htumanyan/navien/esphome/components/navien/navien_link.cpp

#include <cmath>

#include "esphome.h"
#include "esphome/core/log.h"
#include "navien.h"


namespace esphome {
namespace navien {

static const char *TAG = "navien.link";

NavienLink *NavienLink::get_instance(NavienUartI *uart) {
  static NavienLink *instance = nullptr;
  if (instance == nullptr) {
    if (uart == nullptr) {
      ESP_LOGE(TAG, "NavienLink UART adapter required on first get_instance call");
      return nullptr;
    }
    instance = new NavienLink(uart);
  } else if (uart != nullptr && instance->uart != uart) {
    ESP_LOGW(TAG, "Ignoring request to replace Navien UART adapter after initialization");
  }
  return instance;
}


bool NavienLink::seek_to_marker(){
  if (uart == nullptr) {
    return false;
  }
  uint8_t byte;

  int available = uart->available();
  for (int i = 0; i < available; i++){
    uart->peek_byte(&byte);
    if (byte == PACKET_MARKER)
      return true;
    
    uart->read_byte(&byte);
  }
  return false;
}


void NavienLink::parse_control_packet(){
  ESP_LOGV(TAG, "Got Control Packet => %d bytes", this->recv_buffer.hdr.len + HDR_SIZE);
  if (!this->other_navilink_installed
      && this->recv_buffer.hdr.len == NAVILINK_PRESENT[offsetof(HEADER, len)]
      && std::memcmp(this->recv_buffer.raw_data, NAVILINK_PRESENT, sizeof(NAVILINK_PRESENT)) == 0){
    /* This is a NAVILINK_PRESENT_PKT that wasn't sent by us, so anothe NaviLink is also hooked up */
    ESP_LOGW(TAG, "Detected NAVILINK_PRESENT packet from another NaviLink device, will stop sending NAVILINK_PRESENT packets until rebooted %d", sizeof(NAVILINK_PRESENT));
    this->other_navilink_installed = true;
  }
  //  Navien::print_buffer(this->recv_buffer.raw_data, this->recv_buffer.hdr.len + HDR_SIZE);
}
  
void NavienLink::parse_status_packet(){
  switch(this->recv_buffer.hdr.dst){
  case PACKET_DST_WATER:
    ESP_LOGD(TAG, "SRC:0x%02X B8: 0x%02X, B32: 0x%02X, r_enabled: 0x%02X",
             this->recv_buffer.hdr.src,
             this->recv_buffer.water.unknown_06,
             this->recv_buffer.water.unknown_32,
             this->recv_buffer.water.recirculation_enabled);
    for (uint8_t i = 0; i < NAVIEN_CASCADE_MAX; ++i)
      if (visitors_[i]) visitors_[i]->on_water(recv_buffer.water, recv_buffer.hdr.src);
    break;
  case PACKET_DST_GAS:
    ESP_LOGD(TAG, "SRC:0x%02X => Gas", this->recv_buffer.hdr.src);
    for (uint8_t i = 0; i < NAVIEN_CASCADE_MAX; ++i)
      if (visitors_[i]) visitors_[i]->on_gas(recv_buffer.gas, recv_buffer.hdr.src);
    break;
  }
}
  
void NavienLink::parse_packet(){
  uint8_t crc_c = 0x00;
  uint8_t crc_r = 0x00;

  //NavienLink::print_buffer(this->recv_buffer.raw_data, HDR_SIZE + this->recv_buffer.hdr.len + 1);
  crc_r = this->recv_buffer.raw_data[HDR_SIZE + this->recv_buffer.hdr.len];
  
  switch(this->recv_buffer.hdr.direction){
  case PACKET_DIR_STATUS: {
    uint16_t seed;
    if (this->recv_buffer.hdr.src == PACKET_SRC_STATUS) {
      seed = CHECKSUM_SEED_4B;
    } else {
      seed = CHECKSUM_SEED_62;
    }
    crc_c = NavienLink::checksum(this->recv_buffer.raw_data, HDR_SIZE + this->recv_buffer.hdr.len, seed);
    if (crc_c != crc_r){
      ESP_LOGE(TAG, "SRC:0x%02X Status Packet checksum error: 0x%02X (calc) != 0x%02X (recv), seed=0x%02X", this->recv_buffer.hdr.src, crc_c, crc_r, seed);
      NavienLink::print_buffer(this->recv_buffer.raw_data, HDR_SIZE + this->recv_buffer.hdr.len + 1);
      break;
    }
    parse_status_packet();
    break;
  }
  case PACKET_DIR_CONTROL:
  /**
   * The condition below was obsrved in cascade setup where there are lots of 
   * messages, apparently between Navien units and that have some other checksum algorithm that 
   * we're yet to discover. For now we simply ignore those packets. 
   */
    if (this->recv_buffer.hdr.src != PACKET_SRC_CONTROL) {
      ESP_LOGD(TAG, "Control packet from SRC:0x%02X - we don't know how to handle it yet", this->recv_buffer.hdr.src);
      return;
    }
    crc_c = NavienLink::checksum(this->recv_buffer.raw_data, HDR_SIZE + this->recv_buffer.hdr.len, CHECKSUM_SEED_62);
    if (crc_c != crc_r){
      ESP_LOGE(TAG, "SRC:0x%02X Control Packet checksum error: 0x%02X (calc) != 0x%02X (recv), seed=0x%02X", this->recv_buffer.hdr.src, crc_c, crc_r, CHECKSUM_SEED_62);
      this->on_error();
      NavienLink::print_buffer(this->recv_buffer.raw_data, HDR_SIZE + this->recv_buffer.hdr.len + 1);
      break;
    }
    parse_control_packet();
    break;
  }

  //  ESP_LOGV(TAG, "Calculated checksum over %d bytes => 0x%02X", HDR_SIZE + this->recv_buffer.hdr.len, crc);

}


void NavienLink::on_error() {
  ESP_LOGD(TAG, "Notifying visitors of communication error");
  for (uint8_t i = 0; i < NAVIEN_CASCADE_MAX; ++i) {
    if (visitors_[i]) {
      visitors_[i]->on_error();
    }
  }
}

  
void NavienLink::receive() {
  if (uart == nullptr) {
    ESP_LOGE(TAG, "UART pointer is null; skipping receive");
    return;
  }

  int available = uart->available();
  if (!available) {
    return;
  }

  ESP_LOGV(TAG, "%d bytes available", available);
  while (available) {
    switch (this->recv_state) {
      case INITIAL:
        if (this->seek_to_marker()) {
          this->recv_state = MARKER_FOUND;
          ESP_LOGV(TAG, "Marker Found");
          break;
        }
        // No marker found and no data left to read. Exit and wait for more bytes to come.
        return;
      case MARKER_FOUND:
        available = uart->available();
        if (available < HDR_SIZE) {
          ESP_LOGV(TAG, "Only %d bytes available - less than header size", available);
          return;
        }
        if (!uart->read_array(this->recv_buffer.raw_data, HDR_SIZE)) {
          ESP_LOGW(TAG, "Failed to read header");
          this->on_error();
          break;
        }
        this->recv_state = HEADER_PARSED;
        ESP_LOGV(TAG, "Parsed header. %d bytes of body left", this->recv_buffer.hdr.len);
        // fall through
      case HEADER_PARSED: {
        available = uart->available();

        // +1 here is for the checksum - it is in the last byte
        uint8_t len = this->recv_buffer.hdr.len + 1;
        if (available < len) {
          ESP_LOGV(TAG, "Only %d data bytes available - less than len", available);
          return;
        }
        if (!uart->read_array(this->recv_buffer.raw_data + HDR_SIZE, len)) {
          ESP_LOGW(TAG, "Failed to read %d bytes", len);
          this->on_error();
          break;
        }
        ESP_LOGV(TAG, "Got Packet => %d bytes", len + HDR_SIZE);

        if (!this->cmd_buffer.empty()) {
          // There are queued commands. Only send when we are sure the bus is clear to avoid collisions.
          if (!this->other_navilink_installed || std::memcmp(this->recv_buffer.raw_data, NAVILINK_PRESENT, 5) == 0) {
            NAVIEN_CMD cmd = cmd_buffer.back();
            cmd_buffer.pop_back();
            uart->write_array(cmd.buffer, cmd.len);
            // NavienLink::print_buffer(cmd.buffer, cmd.len);
          }
        } else {
          if (!this->other_navilink_installed) {
            // If there's no pending command, send a NAVILINK_PRESENT packet so the unit knows we're here.
            // When the unit is in an automatic recirculation mode, this tell is that we're controlling 
            // when it does and does not recirculate (and it triggers the "Recirculation settings must be 
            // configured through the NaviLink app" message on the unit's front panel when you try to
            // change the recirculation setting)
            uart->write_array(NAVILINK_PRESENT, sizeof(NAVILINK_PRESENT));
            // NavienLink::print_buffer(NAVILINK_PRESENT, sizeof(NAVILINK_PRESENT));
          }
        }

        // Navien::print_buffer(this->recv_buffer.raw_data, len + HDR_SIZE);
        this->parse_packet();
        available = uart->available();
        this->recv_state = INITIAL;
        break;
      }
    }
  }
}

void NavienLink::send_cmd(const uint8_t * buffer, uint8_t len, uint8_t tries){
  // Send multiple times by default. In experiments I've noticed
  // that sending once does not always work and that
  // the NaviLink sends the commands multiple times
  for (uint8_t i = 0; i < tries; i++) {
    this->cmd_buffer.push_front(NAVIEN_CMD(buffer, len));
  }
}
  
void NavienLink::send_turn_on_cmd(){
  this->send_cmd(TURN_ON_CMD, sizeof(TURN_ON_CMD));
}

void NavienLink::send_turn_off_cmd(){
  this->send_cmd(TURN_OFF_CMD, sizeof(TURN_OFF_CMD));
}

void NavienLink::send_hot_button_cmd(){
  this->send_cmd(HOT_BUTTON_PRESS_CMD, sizeof(HOT_BUTTON_PRESS_CMD));
  this->send_cmd(HOT_BUTTON_RELSE_CMD, sizeof(HOT_BUTTON_RELSE_CMD), 1);
}
  

void NavienLink::send_dhw_set_temp_cmd(float temp){
  uint8_t cmd[19];
  memcpy(cmd, DHW_SET_TEMP_CMD_TEMPLATE, sizeof(DHW_SET_TEMP_CMD_TEMPLATE));
  cmd[9] = temp * 2 + 0.5;
  cmd[18] = NavienLink::checksum(cmd, sizeof(DHW_SET_TEMP_CMD_TEMPLATE) - 1, CHECKSUM_SEED_62);

  NavienLink::print_buffer(cmd, sizeof(DHW_SET_TEMP_CMD_TEMPLATE));
  this->send_cmd(cmd, sizeof(DHW_SET_TEMP_CMD_TEMPLATE));
}

/**
 * Space-heating setpoint (combi / boiler units).
 *
 * Same 0x4F control packet as the DHW setpoint, with the temperature in
 * byte 10 instead of byte 9 (deg C * 2). Byte 9 stays 0x00, which the unit
 * treats as "leave DHW unchanged" - the mirror of DHW commands carrying 0x00
 * in byte 10, which never move the SH setpoint.
 *
 * Verified on an NCB-240/110H (device type NCB_H, f7 06 framing): commands
 * for 160.7 F, 158.9 F and 156.2 F were each followed by the unit reporting
 * that value in the gas packet's sh_set_temp. Byte 10 is the slot tankless
 * units always leave 0x00.
 */
void NavienLink::send_sh_set_temp_cmd(float temp){
  uint8_t cmd[19];
  memcpy(cmd, DHW_SET_TEMP_CMD_TEMPLATE, sizeof(DHW_SET_TEMP_CMD_TEMPLATE));
  cmd[10] = temp * 2 + 0.5;
  cmd[18] = NavienLink::checksum(cmd, sizeof(DHW_SET_TEMP_CMD_TEMPLATE) - 1, CHECKSUM_SEED_62);

  NavienLink::print_buffer(cmd, sizeof(DHW_SET_TEMP_CMD_TEMPLATE));
  this->send_cmd(cmd, sizeof(DHW_SET_TEMP_CMD_TEMPLATE));
}

void NavienLink::send_scheduled_recirculation_on_cmd(){
  this->send_cmd(SCHEDULED_RECIRC_ON_CMD, sizeof(SCHEDULED_RECIRC_ON_CMD));
}

void NavienLink::send_scheduled_recirculation_off_cmd(){
  this->send_cmd(SCHEDULED_RECIRC_OFF_CMD, sizeof(SCHEDULED_RECIRC_OFF_CMD));
}

/**
 * Convert flow units to liters/min values
 * flow is reported as 0.1 liter units.
 */
float NavienLink::flow2lpm(uint8_t f){
  return (float)f / 10.f;
}
  
/**
 * Convert flow units to GPM values
 * flow is reported as 0.1 liter units.
 * we're calculating flow in liters/min and then
 * converting to gallons resulting in GPM (Gallons Per Min)
 */
float NavienLink::flow2gpm(uint8_t f){
  return  (float)f / 10.f / 3.785f;
}

float NavienLink::t2c(uint8_t c){
  return (float)c / 2.f;
}

float NavienLink::ot2c(uint8_t c){
  // Value when no probe is connected.
  // Decodes to right at low end of many 10k thermistors (-30C) so probably min reportable?
  if (c == 0x9E) {
    return NAN;
  }
  float sign = c & 0x80 ? -1 : 1;
  float mag = c & 0x7F;
  return sign * mag;
}
  
uint8_t NavienLink::t2f(uint8_t c){
  float f = c;

  f /= 2;

  f = f * 9.f / 5.f + 32.f;

  return (uint8_t)round(f);
}

  
void NavienLink::print_buffer(const uint8_t *data, size_t length) {
   char hex_buffer[100];
   hex_buffer[(3 * 32) + 1] = 0;
   for (size_t i = 0; i < length; i++) {
     size_t offset = 3 * (i % 32);
     snprintf(&hex_buffer[offset], sizeof(hex_buffer) - offset, "%02X ", data[i]);
     if (i % 32 == 31) {
       ESP_LOGI(TAG, "   %s", hex_buffer);
     }
   }
   if (length % 32) {
     // null terminate if incomplete line
     hex_buffer[3 * (length % 32) + 2] = 0;
     ESP_LOGI(TAG, "   %s", hex_buffer);
   }
 }

  
uint8_t NavienLink::checksum(const uint8_t * buffer, uint8_t len, uint16_t seed){  
  uint16_t result;

  if (len < 2) {
    result = 0x00;
  }
  else {
    result = 0xff;

    for (uint i = 0; i < len; i++){
      result = result << 1;

      if (result > 0xff){
	result = (result & 0xff) ^ seed;
      }

      // this is important!!
      // the checksum is calculated
      // based on the lower byte, i.e.
      // only the lower byte is XOR-ed
      result = ((uint8_t)result) ^ (uint16_t)buffer[i];
    }
  }
  return result;
}


  
}  // namespace navien
}  // namespace esphome
