htumanyan/navien/esphome/components/navien/navien_link_esp.h

#pragma once

// NavienLinkEsp has been deprecated. This header remains for backward compatibility
// and intentionally leaves the implementation empty.

namespace esphome {
namespace navien {

class NavienLinkEsp {
 public:
  NavienLinkEsp() = default;
};

}  // namespace navien
}  // namespace esphome
